pdlhcontadero-coder/AdquisiciondeDatos/Diseño 3D - Inventor/Planos Finales Sistema de Monitoreo/Planos en imagen/004 Plano 4 - Módulo de Conductividad (Tapa).jpg

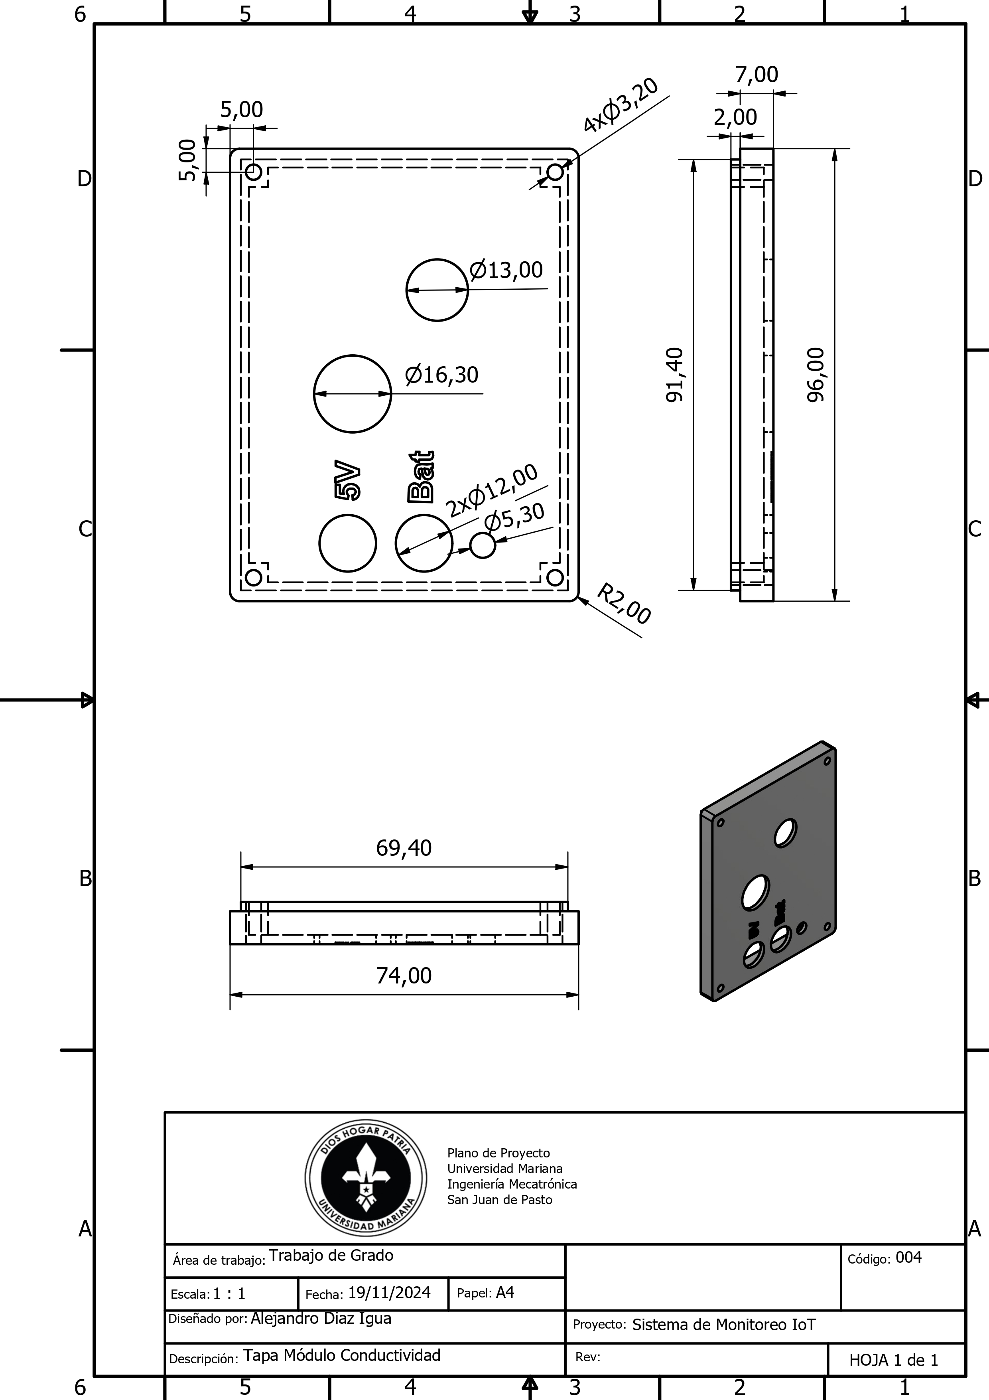
Diseño 3D - Inventor/Planos Finales Sistema de Monitoreo/Planos en imagen/004 Plano 4 - Módulo de Conductividad (Tapa).jpg
