pdlhcontadero-coder/AdquisiciondeDatos/Diseño 3D - Inventor/Planos Finales Sistema de Monitoreo/Planos en imagen/005 Plano 5 - Módulo de pH (Caja).jpg

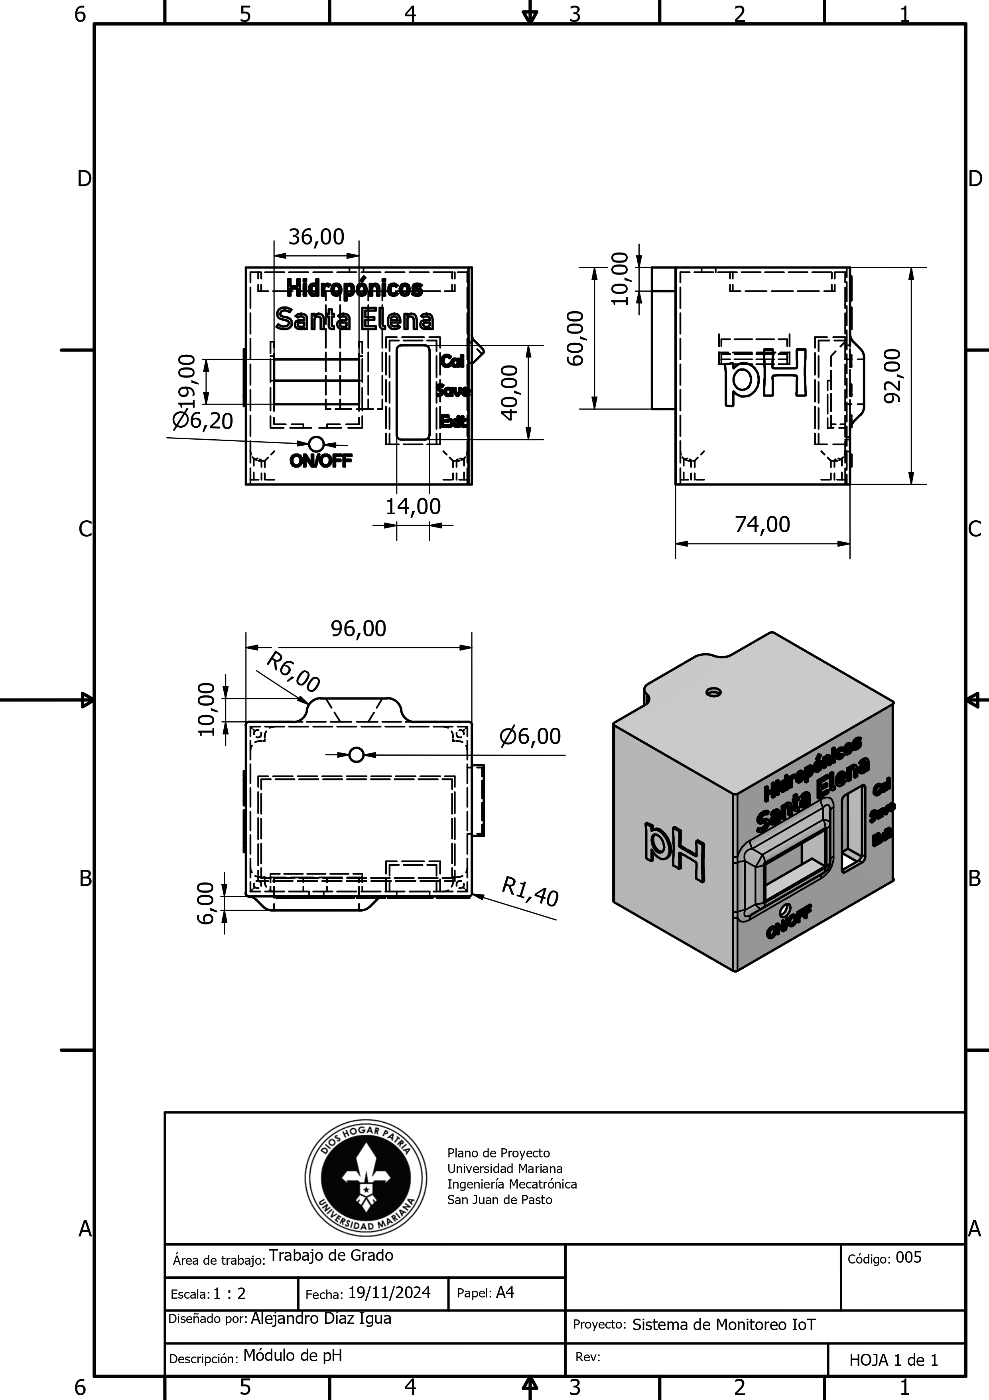
Diseño 3D - Inventor/Planos Finales Sistema de Monitoreo/Planos en imagen/005 Plano 5 - Módulo de pH (Caja).jpg
