pdlhcontadero-coder/AdquisiciondeDatos/Diseño 3D - Inventor/Planos Finales Sistema de Monitoreo/Planos en imagen/007 Plano 7 - Módulo de Nivel de Tanque (Caja).jpg

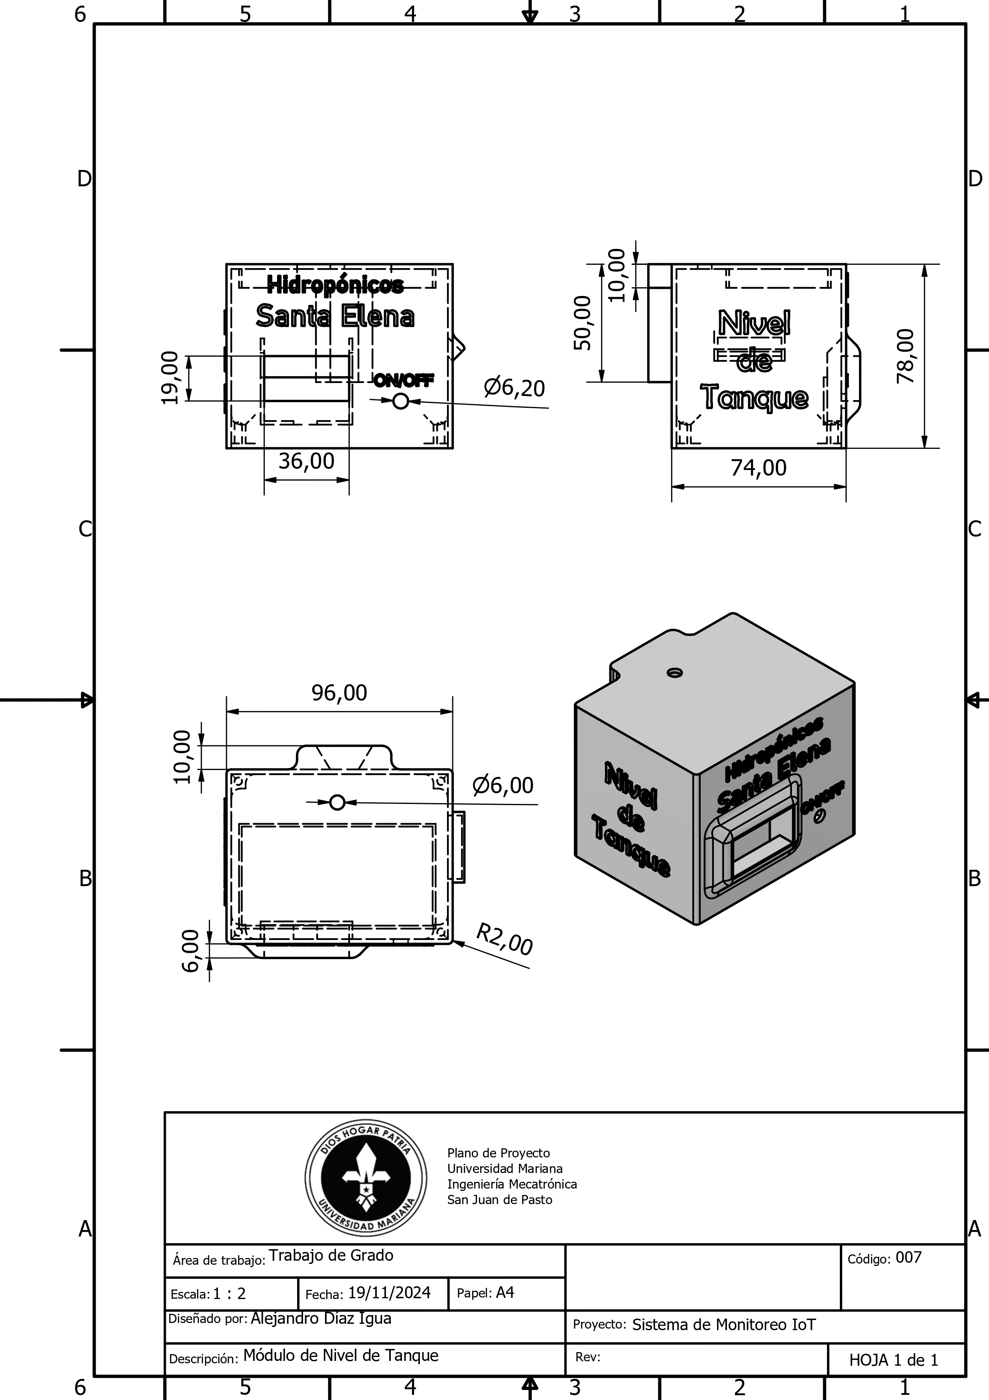
Diseño 3D - Inventor/Planos Finales Sistema de Monitoreo/Planos en imagen/007 Plano 7 - Módulo de Nivel de Tanque (Caja).jpg
