pdlhcontadero-coder/AdquisiciondeDatos/Diseño 3D - Inventor/Planos Finales Sistema de Monitoreo/Planos en imagen/008 Plano 8 - Módulo de Nivel de Tanque (Tapa).jpg

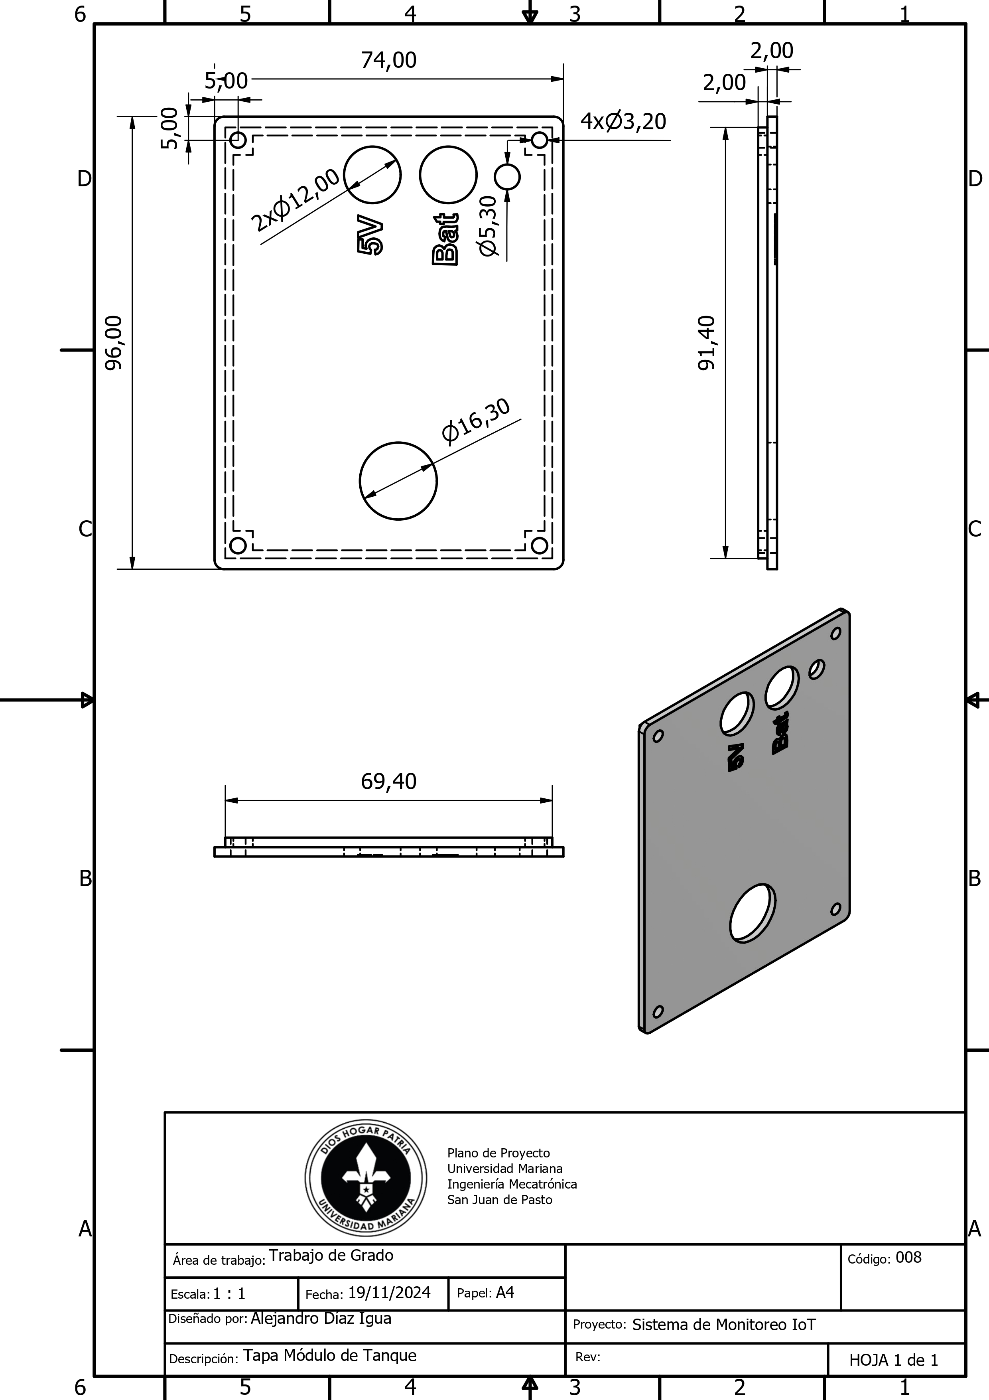
Diseño 3D - Inventor/Planos Finales Sistema de Monitoreo/Planos en imagen/008 Plano 8 - Módulo de Nivel de Tanque (Tapa).jpg
