pdlhcontadero-coder/AdquisiciondeDatos/Diseño 3D - Inventor/Planos Finales Sistema de Monitoreo/Planos en imagen/012 Plano 12 - Soporte Panel Solar 1.jpg

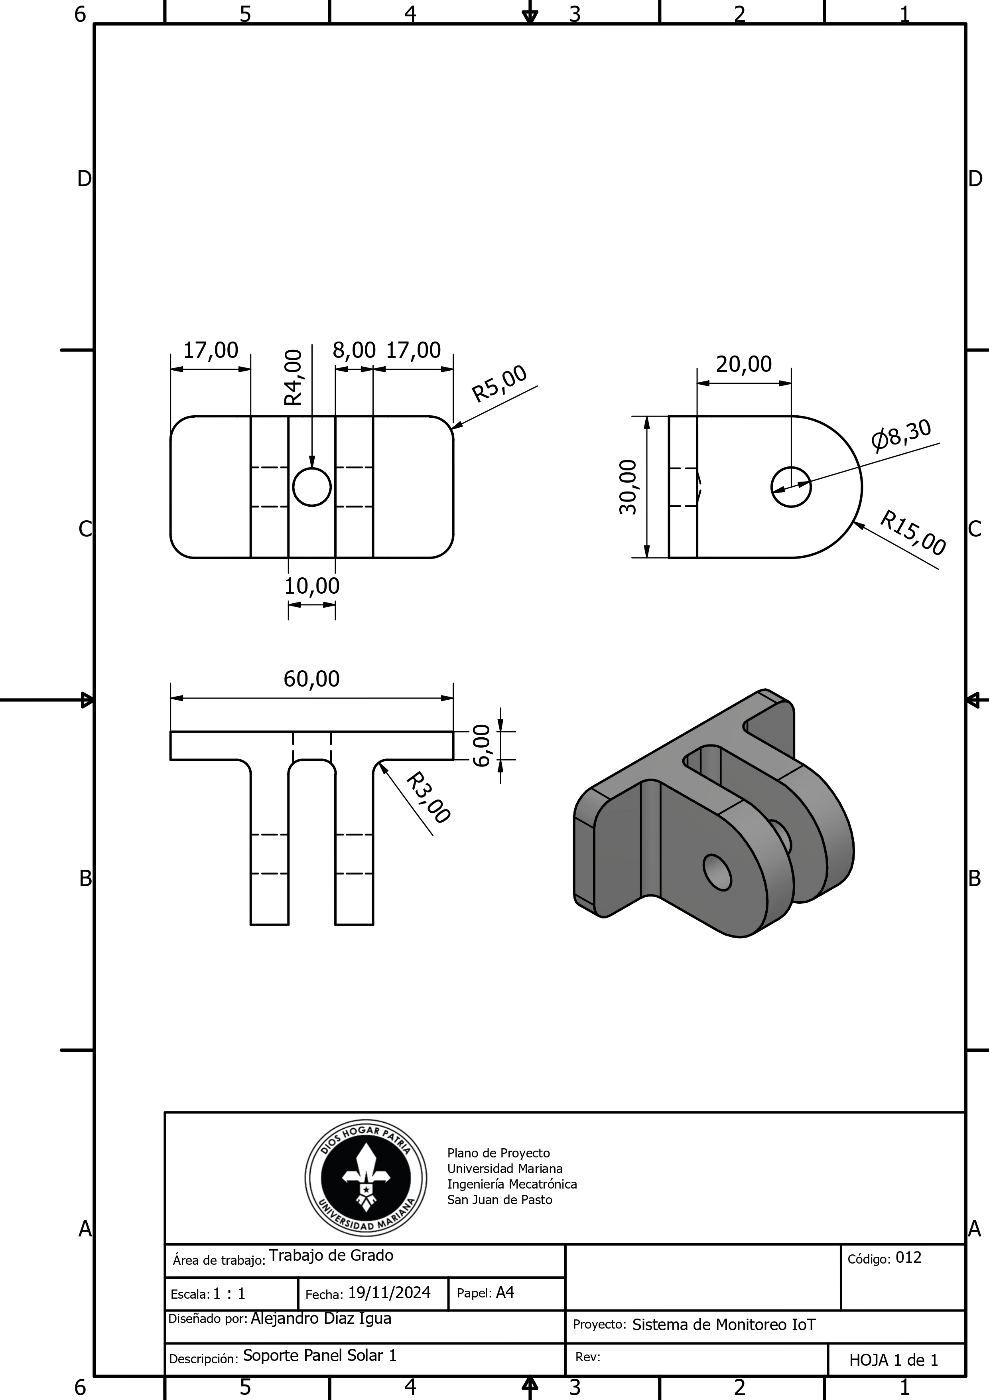
Diseño 3D - Inventor/Planos Finales Sistema de Monitoreo/Planos en imagen/012 Plano 12 - Soporte Panel Solar 1.jpg
