pdlhcontadero-coder/AdquisiciondeDatos/Diseño 3D - Inventor/Planos Finales Sistema de Monitoreo/Planos en imagen/013 Plano 13 - Soporte Panel Solar 2.jpg

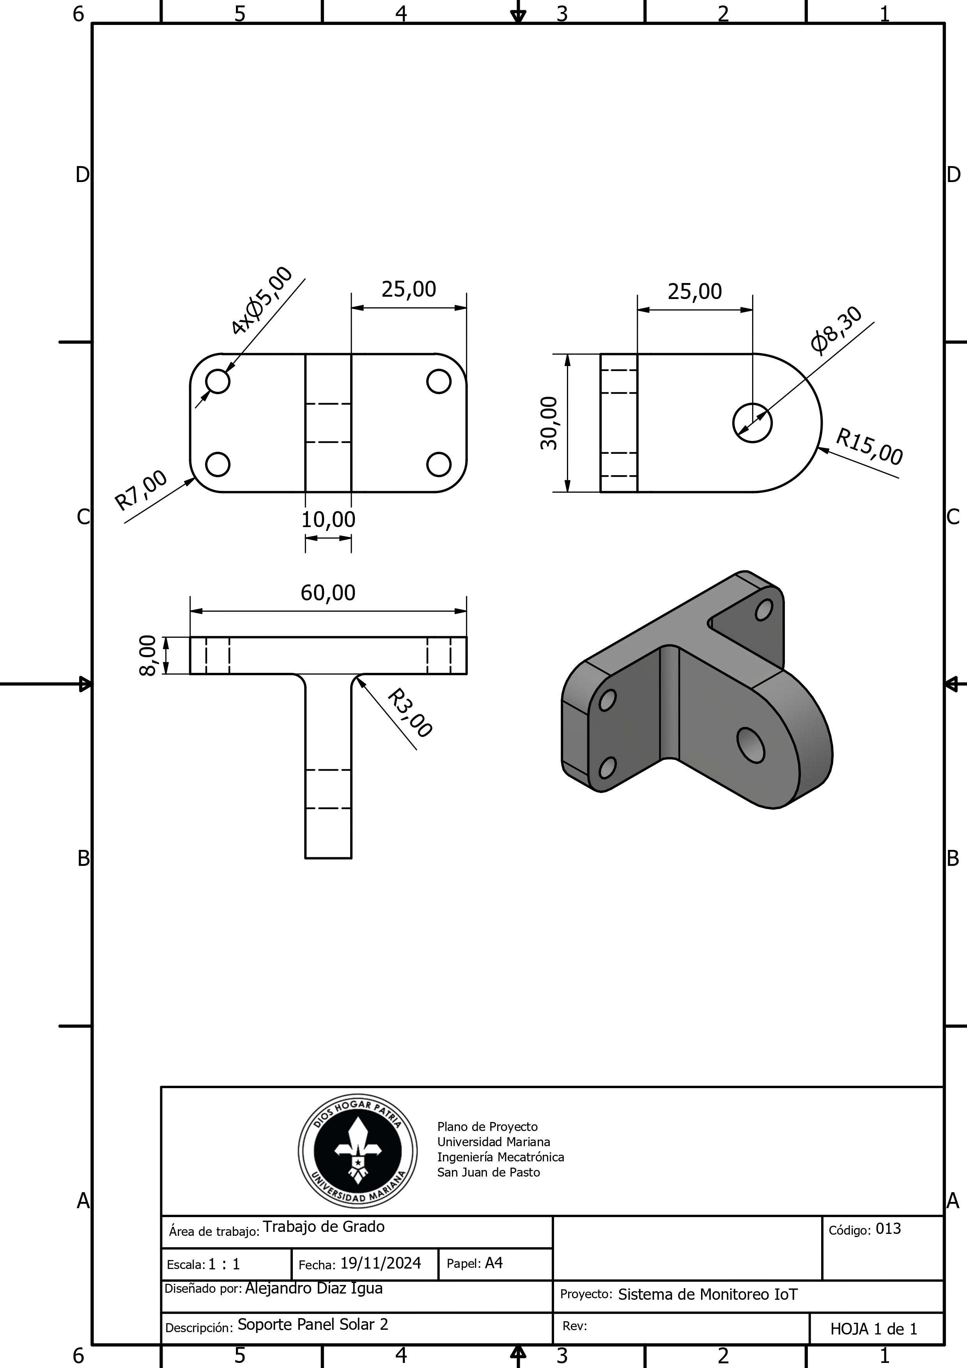
Diseño 3D - Inventor/Planos Finales Sistema de Monitoreo/Planos en imagen/013 Plano 13 - Soporte Panel Solar 2.jpg
