pdlhcontadero-coder/AdquisiciondeDatos/Diseño 3D - Inventor/Planos Finales Sistema de Monitoreo/Planos en imagen/014 Plano 14 - Botón.jpg

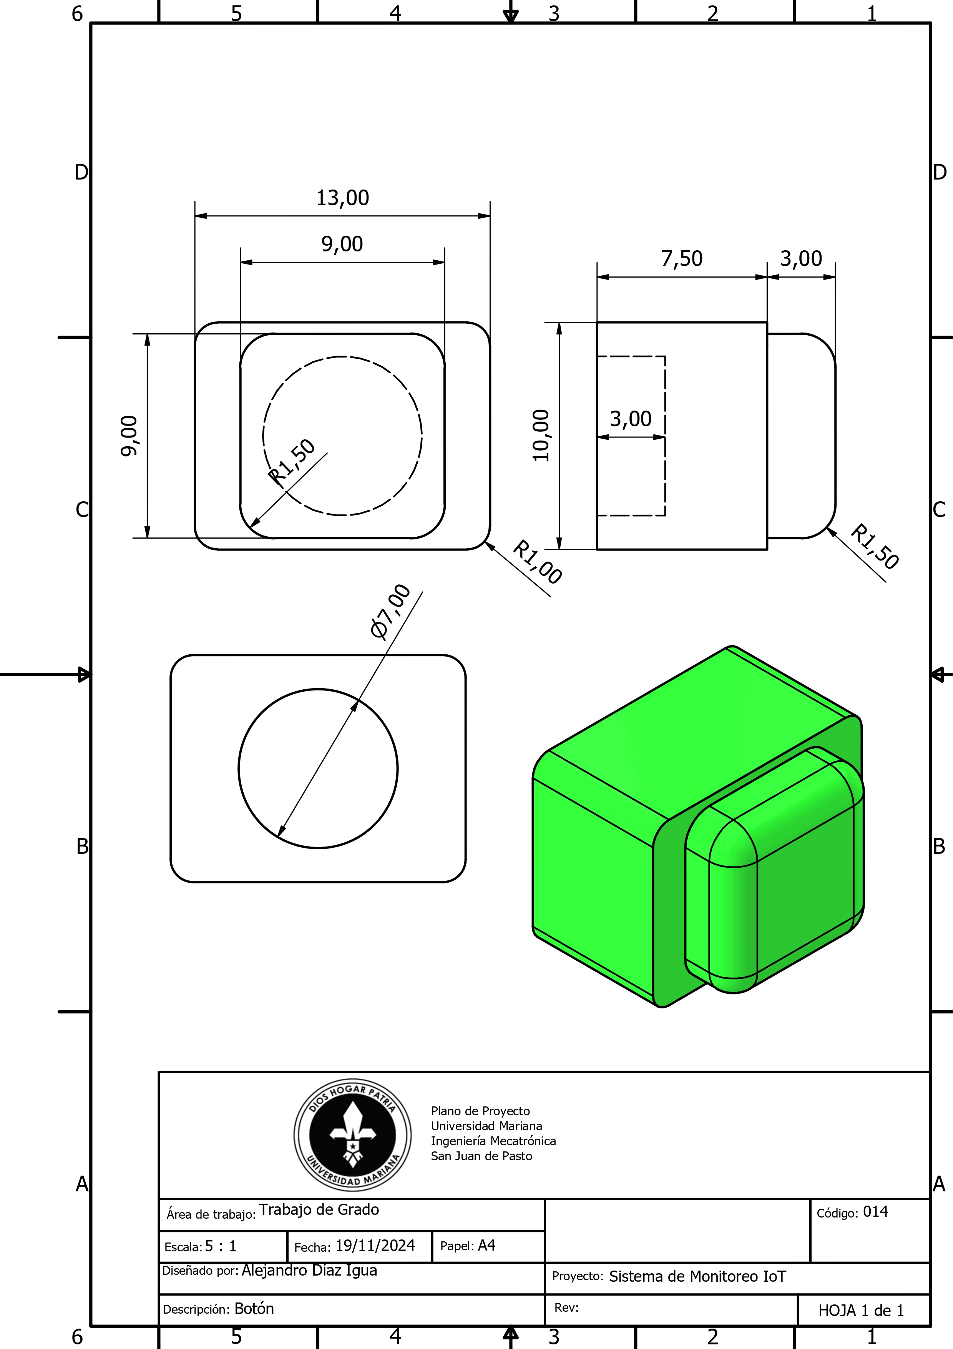
Diseño 3D - Inventor/Planos Finales Sistema de Monitoreo/Planos en imagen/014 Plano 14 - Botón.jpg
