pdlhcontadero-coder/AdquisiciondeDatos/Diseño 3D - Inventor/Planos Finales Sistema de Monitoreo/Planos en imagen/015 Plano 15 - Agarradera Módulo Principal.jpg

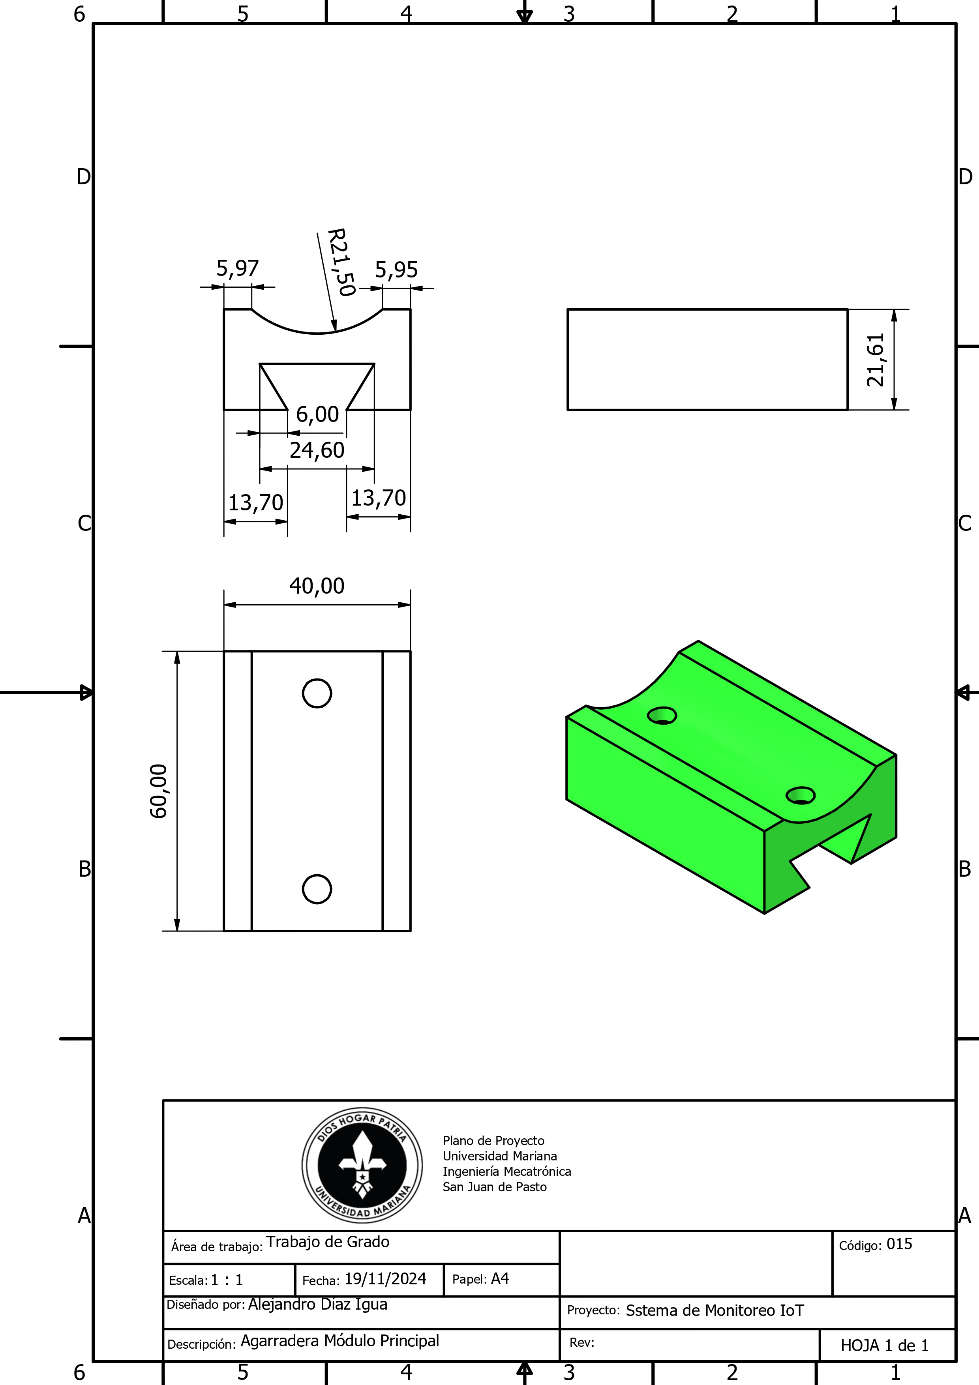
Diseño 3D - Inventor/Planos Finales Sistema de Monitoreo/Planos en imagen/015 Plano 15 - Agarradera Módulo Principal.jpg
