pdlhcontadero-coder/AdquisiciondeDatos/Diseño 3D - Inventor/Planos Finales Sistema de Monitoreo/Planos en imagen/016 Plano 16 - Agarradera 1.jpg

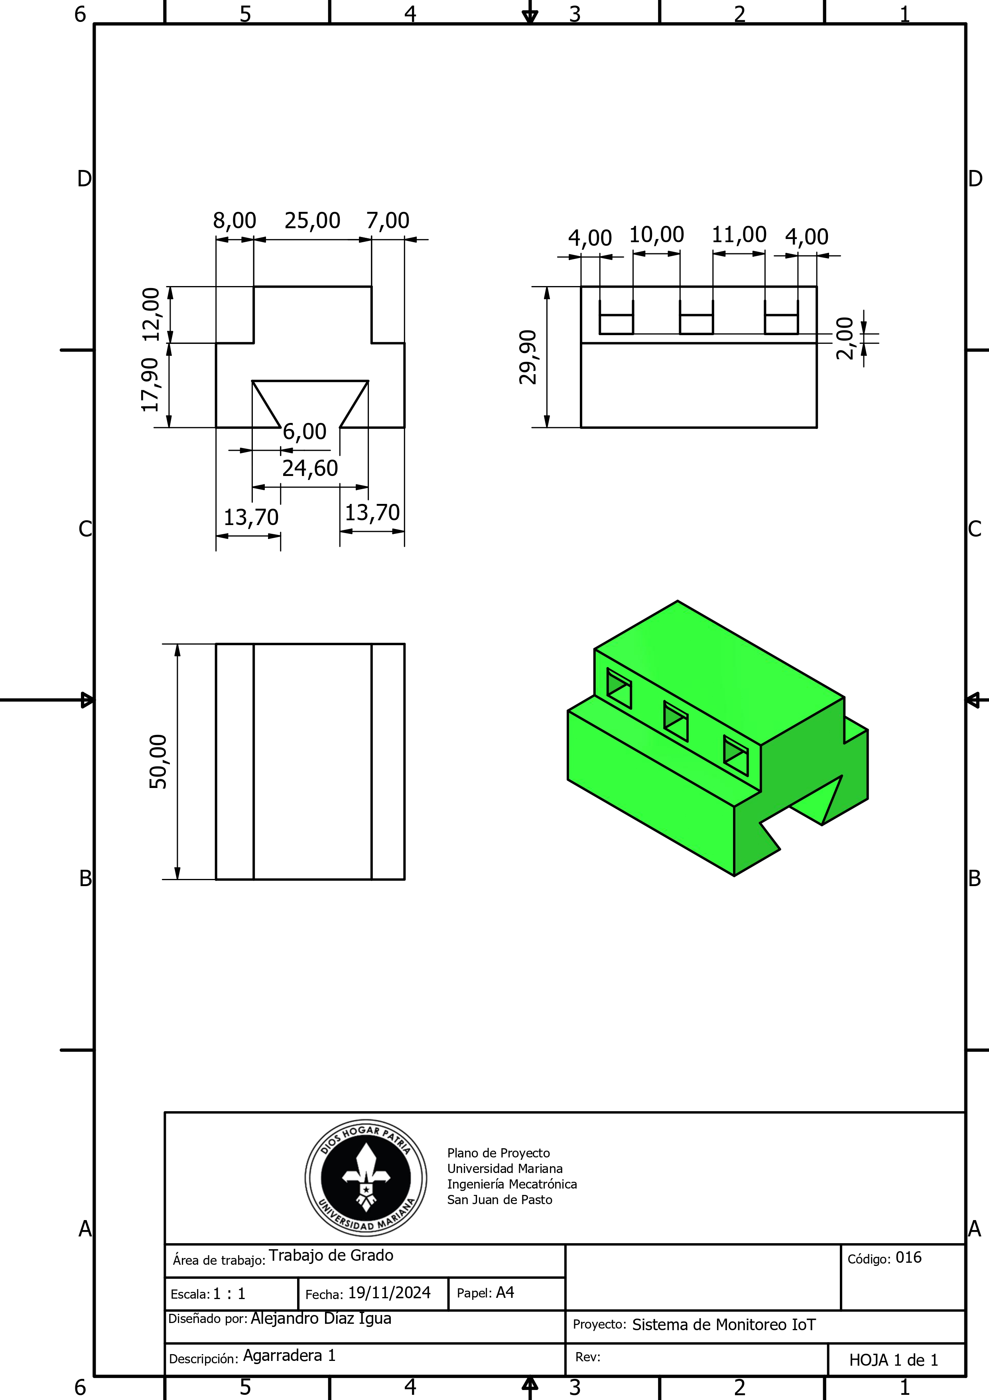
Diseño 3D - Inventor/Planos Finales Sistema de Monitoreo/Planos en imagen/016 Plano 16 - Agarradera 1.jpg
