pdlhcontadero-coder/AdquisiciondeDatos/Diseño 3D - Inventor/Planos Finales Sistema de Monitoreo/Planos en imagen/018 Plano 18 - Adapatador Sensor de Altura.jpg

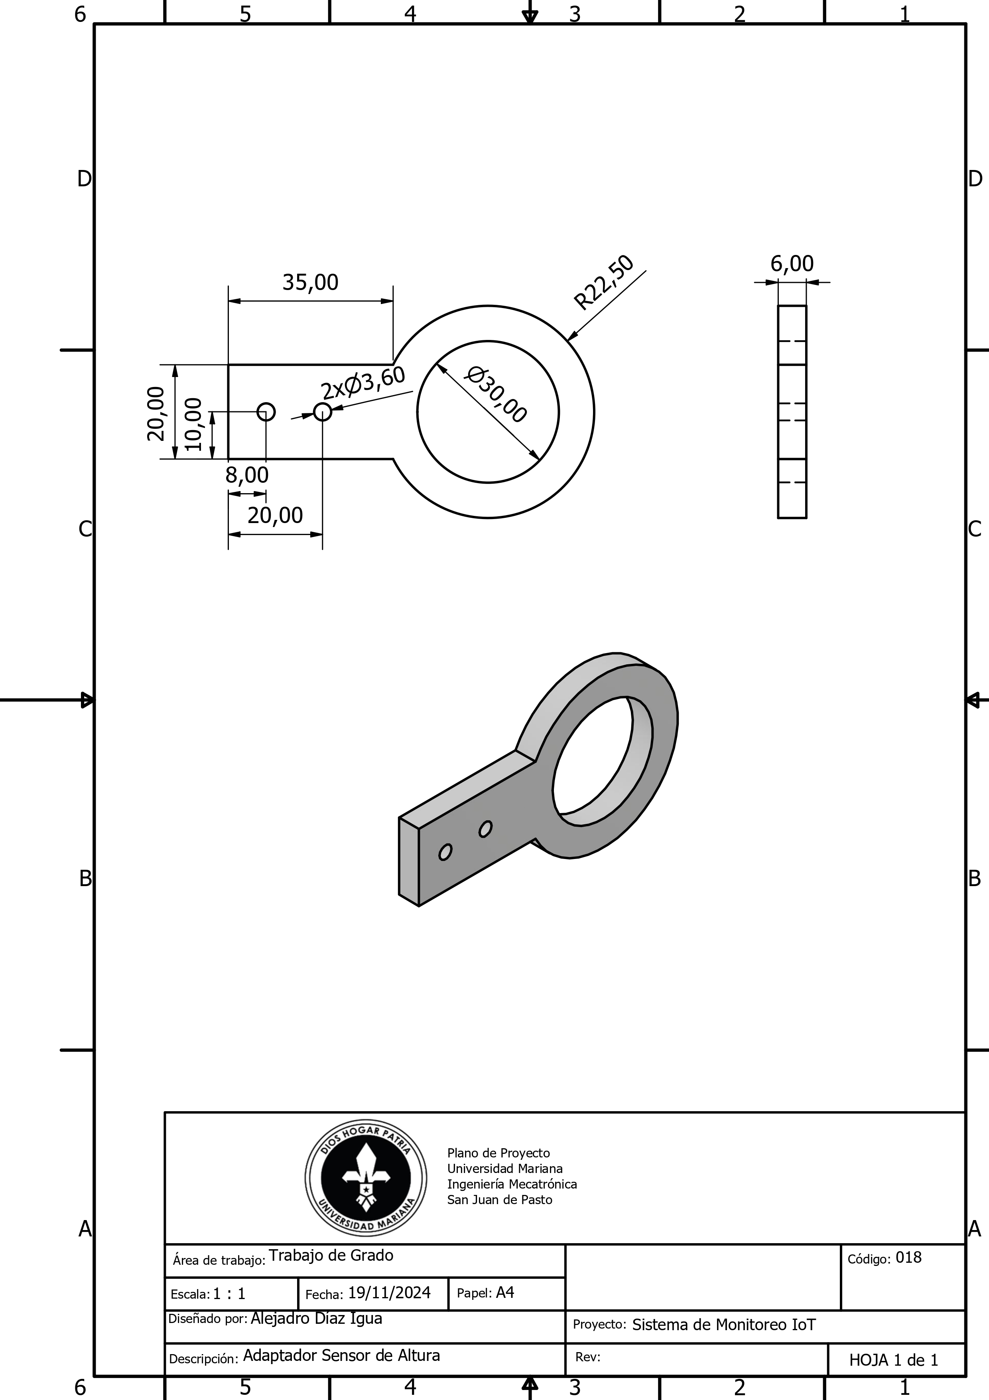
Diseño 3D - Inventor/Planos Finales Sistema de Monitoreo/Planos en imagen/018 Plano 18 - Adapatador Sensor de Altura.jpg
