pdlhcontadero-coder/AdquisiciondeDatos/Diseño 3D - Inventor/Invernadero/Ensamble/Ensamblaje1 ([Principal]).pdf

setPageBoxes("Crop", 0, 0, [0,2000,2000,0]);

TÍTULO N.º DE PIEZA | Ensamblaje1 REVISIÓN DISEÑADOR | PAVILION INGENIERO NOTAS

LA INFORMACIÓN O LOS MATERIALES DE ESTE DOCUMENTO SON PROPIEDAD E INFORMACIÓN RESTRINGIDA O MATERIALES DEL AUTOR. ESTA INFORMACIÓN NO SE PUEDE UTILIZAR, REPRODUCIR, PUBLICAR O REVELAR A TERCEROS SIN AUTORIZACIÓN POR ESCRITO. DEBE UTILIZARSE SOLO PARA LA FABRICACIÓN DE LOS ELEMENTOS ESPECIFICADOS EN EL DOCUMENTO.
