pdlhcontadero-coder/AdquisiciondeDatos/Diseño 3D - Inventor/Planos Finales Sistema de Monitoreo/018 Plano 18 - Adapatador Sensor de Altura.pdf

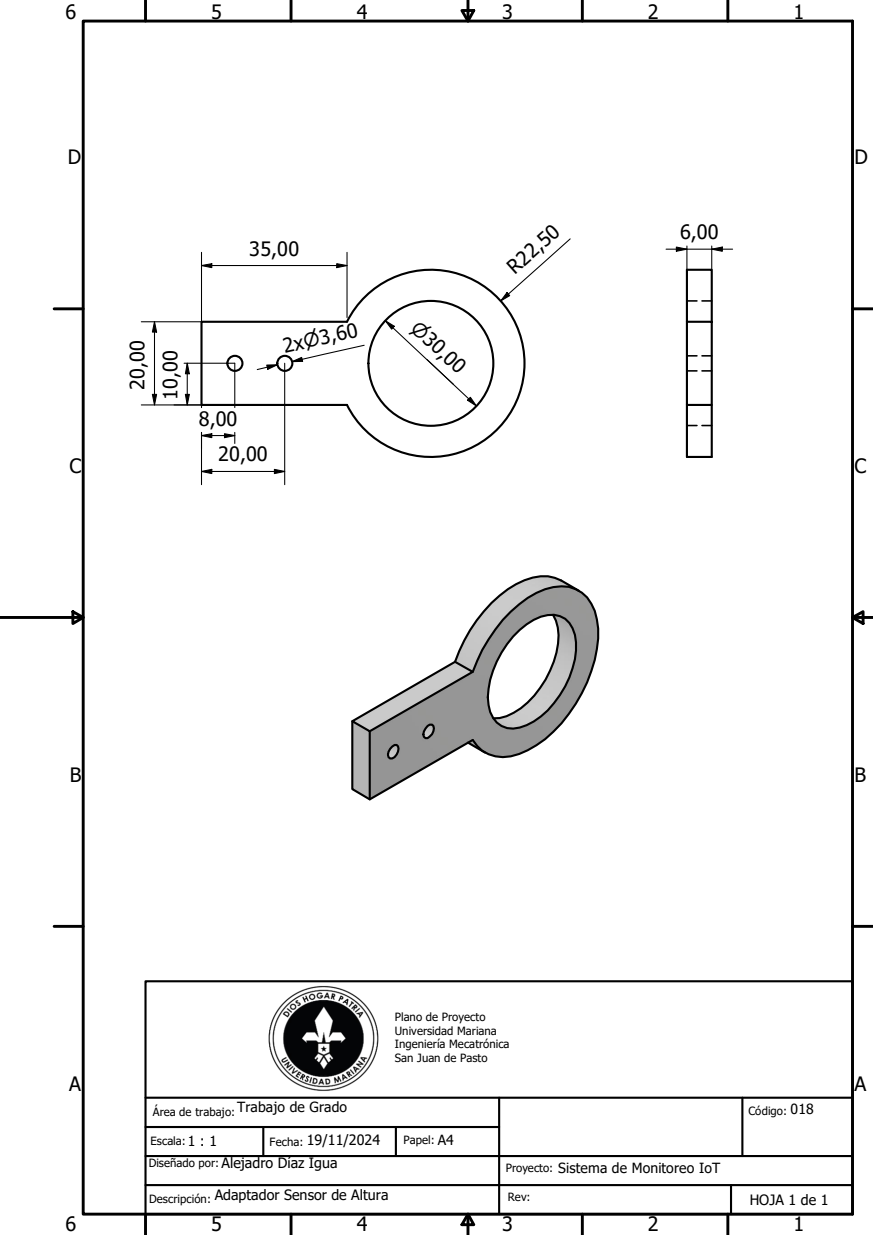
[picture p29: page 1]

Plano de Proyecto
Universidad Mariana
Ingeniería Mecatrónica
San Juan de Pasto

Área de trabajo: Trabajo de Grado | | Código: 018

Escala: 1 : 1 | Fecha: 19/11/2024 | Papel: A4
Diseñado por: Alejadro Díaz Igua | Proyecto: Sistema de Monitoreo IoT

Descripción: Adaptador Sensor de Altura | Rev: | HOJA 1 de 1
