pdlhcontadero-coder/AdquisiciondeDatos/Diseño 3D - Inventor/Planos Finales Sistema de Monitoreo/013 Plano 13 - Soporte Panel Solar 2.pdf

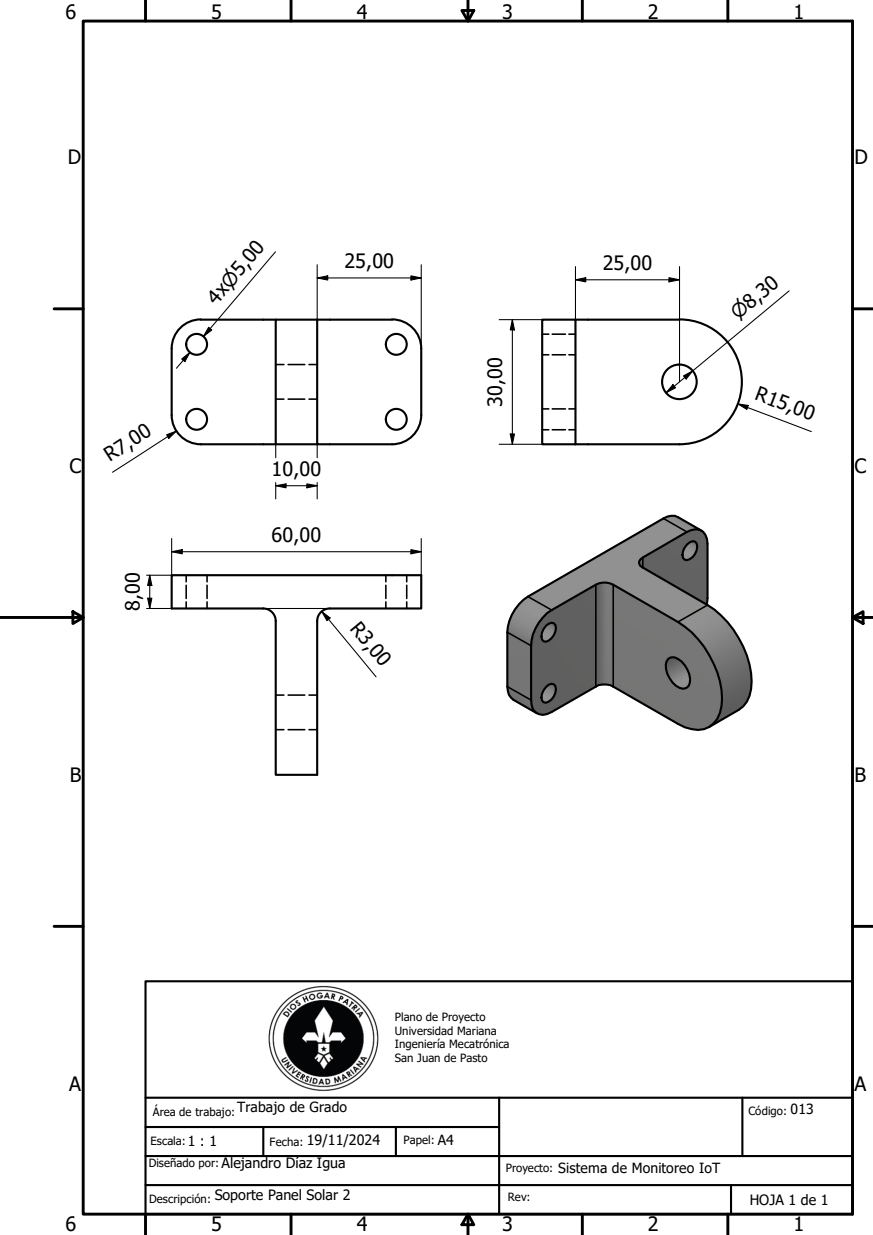
[picture p42: page 1]

Plano de Proyecto
Universidad Mariana
Ingeniería Mecatrónica
San Juan de Pasto

Área de trabajo: Trabajo de Grado | | Código: 013

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

Descripción: Soporte Panel Solar 2 | Rev: | HOJA 1 de 1
