pdlhcontadero-coder/AdquisiciondeDatos/Diseño 3D - Inventor/Planos Finales Sistema de Monitoreo/014 Plano 14 - Botón.pdf

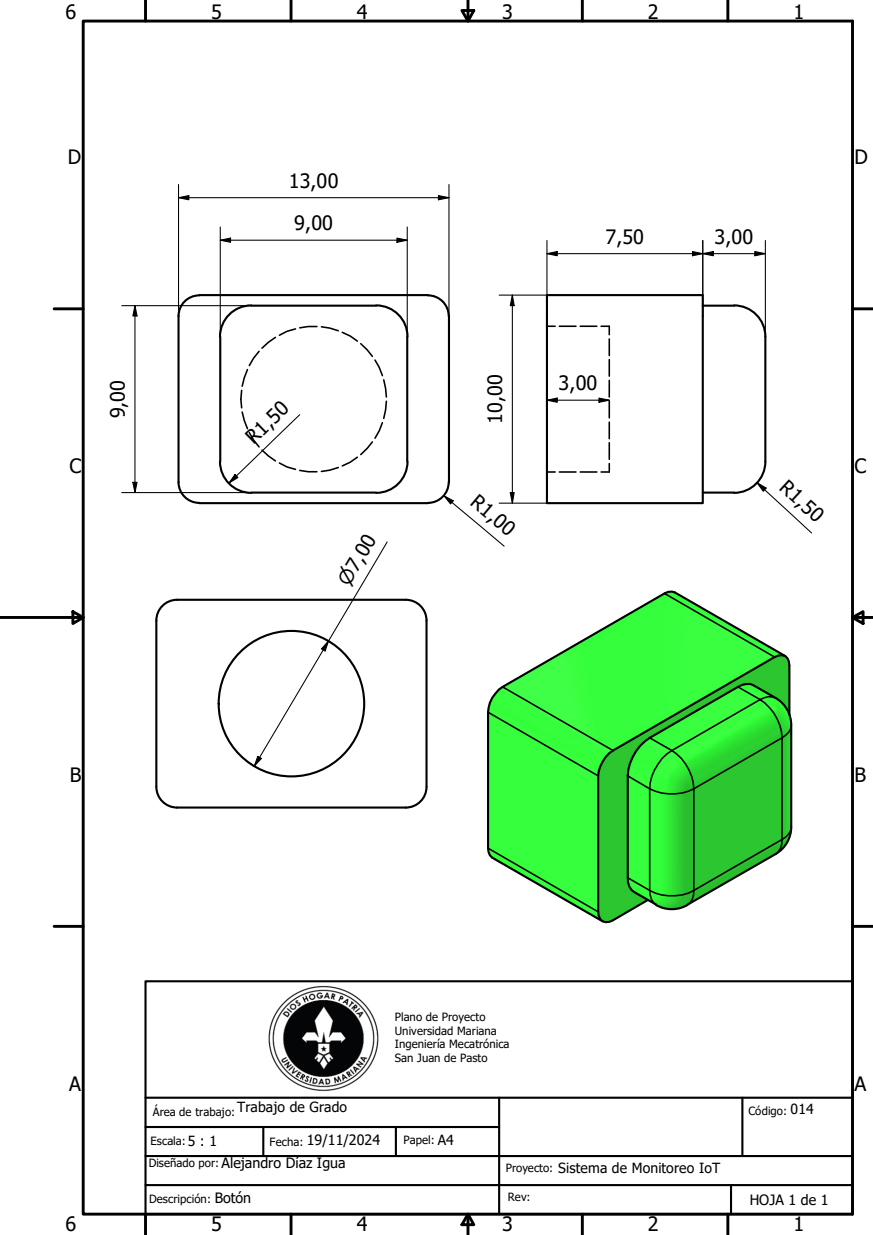
[picture p43: page 1]

Plano de Proyecto
Universidad Mariana
Ingeniería Mecatrónica
San Juan de Pasto

Área de trabajo: Trabajo de Grado | | Código: 014

Escala: 5 : 1 | Fecha: 19/11/2024 | Papel: A4
Diseñado por: Alejandro Díaz Igua | Proyecto: Sistema de Monitoreo IoT

Descripción: Botón | Rev: | HOJA 1 de 1
