pdlhcontadero-coder/AdquisiciondeDatos/Diseño 3D - Inventor/Planos Finales Sistema de Monitoreo/015 Plano 15 - Agarradera Módulo Principal.pdf

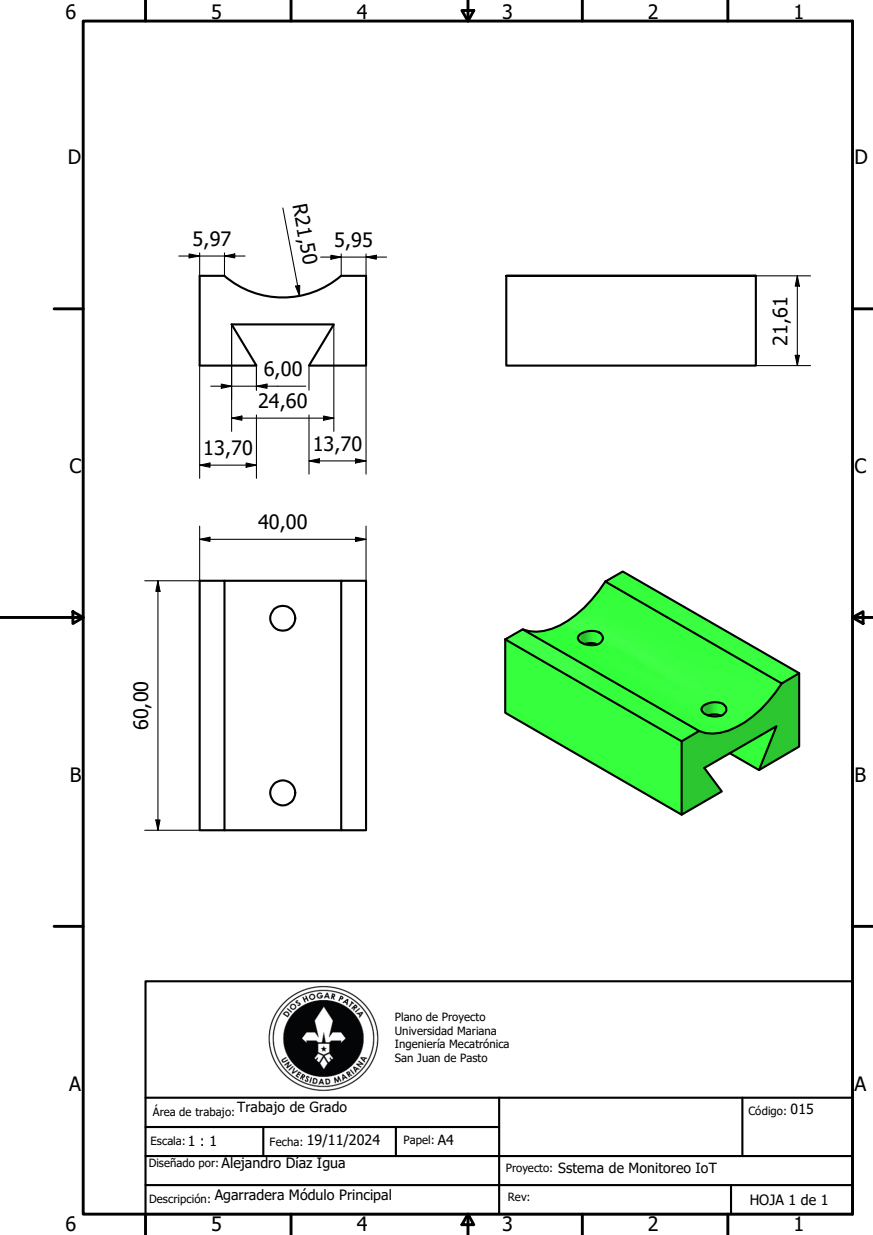
[picture p44: page 1]

Plano de Proyecto
Universidad Mariana
Ingeniería Mecatrónica
San Juan de Pasto

Área de trabajo: Trabajo de Grado | | Código: 015

Escala: 1 : 1 | Fecha: 19/11/2024 | Papel: A4
Diseñado por: Alejandro Díaz Igua | Proyecto: Sstema de Monitoreo IoT

Descripción: Agarradera Módulo Principal | Rev: | HOJA 1 de 1
