pdlhcontadero-coder/AdquisiciondeDatos/Diseño 3D - Inventor/Planos Finales Sistema de Monitoreo/016 Plano 16 - Agarradera 1.pdf

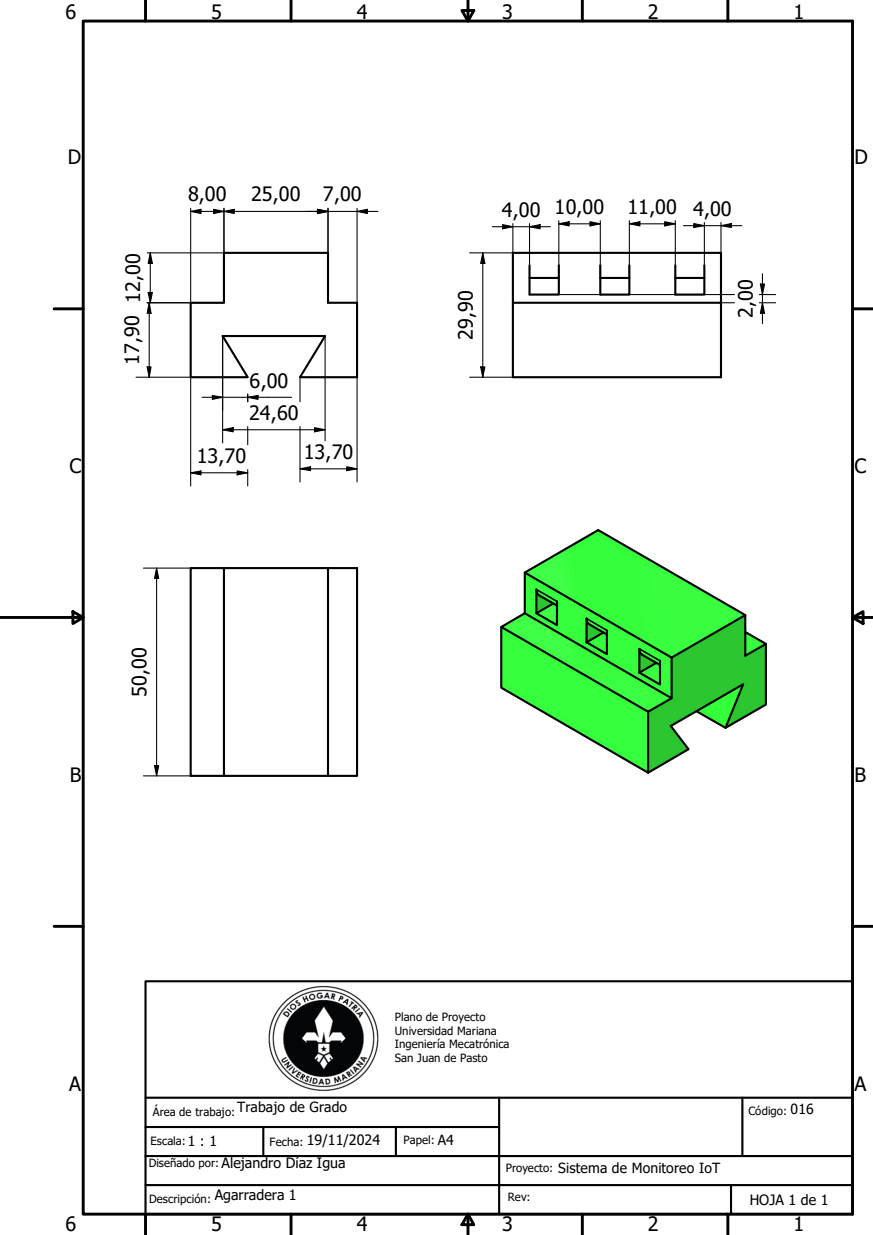
[picture p45: page 1]

Plano de Proyecto
Universidad Mariana
Ingeniería Mecatrónica
San Juan de Pasto

Área de trabajo: Trabajo de Grado | | Código: 016

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

Descripción: Agarradera 1 | Rev: | HOJA 1 de 1
