pdlhcontadero-coder/AdquisiciondeDatos/Diseño 3D - Inventor/Planos Finales Sistema de Monitoreo/017 Plano 17 - Agarradera 2.pdf

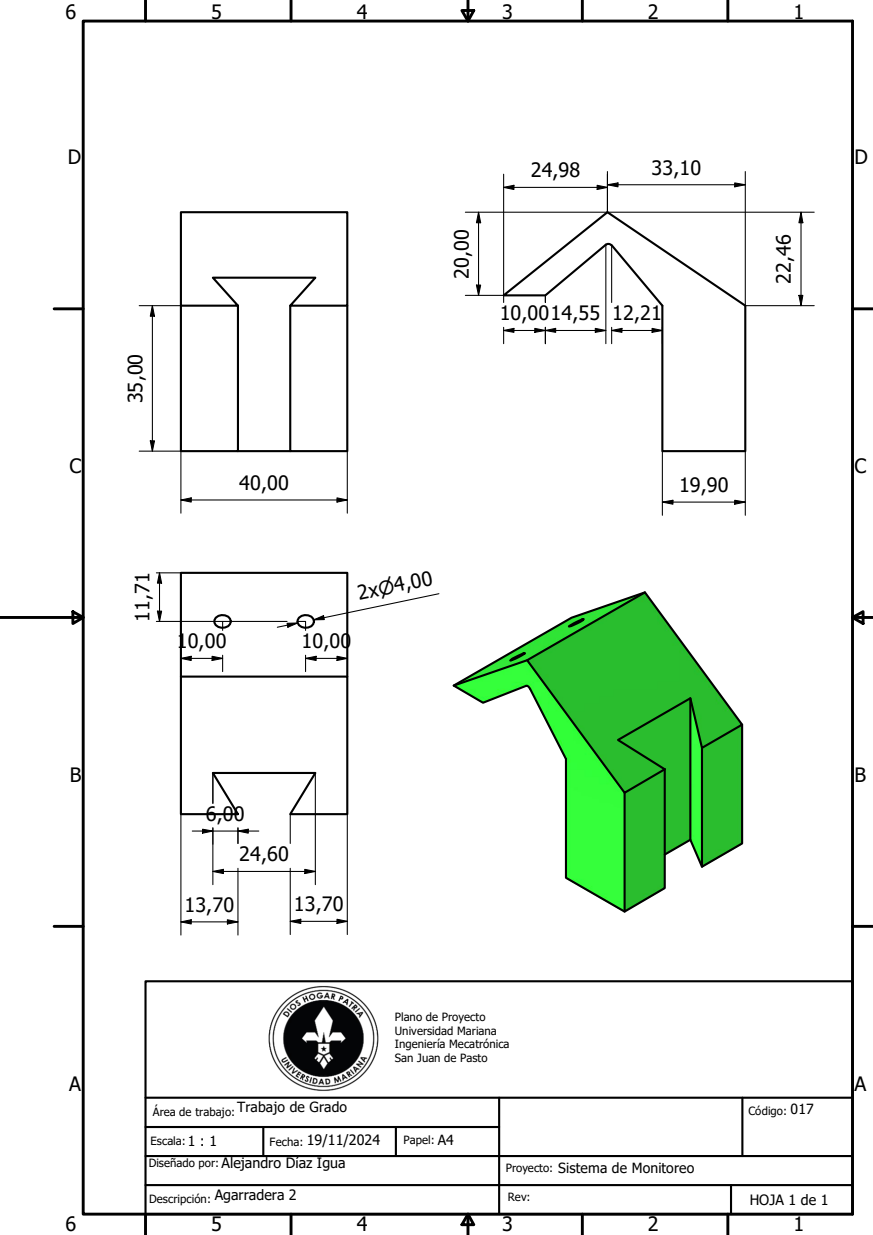
[picture p46: page 1]

Plano de Proyecto
Universidad Mariana
Ingeniería Mecatrónica
San Juan de Pasto

Área de trabajo: Trabajo de Grado | | Código: 017

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

Descripción: Agarradera 2 | Rev: | HOJA 1 de 1
