pdlhcontadero-coder/AdquisiciondeDatos/Diseño 3D - Inventor/Planos Finales Sistema de Monitoreo/Planos Sistema de Monitoreo.pdf

D | D

HOJA 1 de 1; Área de trabajo:; Trabajo de Grado; Escala:; Fecha:; Papel:; Rev:; Descripción:; Módulo Principal

Plano de Proyecto
Universidad Mariana
Ingeniería Mecatrónica
San Juan de Pasto

Código: 001

Diseñado por: Alejandro Díaz Igua

Proyecto: Sistema de Monitoreo IoT

D | 142,30 | D

12,00

Código:

Plano de Proyecto
Universidad Mariana
Ingeniería Mecatrónica
San Juan de Pasto

Área de trabajo: Proyecto de Grado

Descripción: Tapa Módulo Principal

D | D
36,00 | 14,00

Código:

Plano de Proyecto
Universidad Mariana
Ingeniería Mecatrónica
San Juan de Pasto

Área de trabajo: Trabajo de Grado

Descripción: Módulo de Conductividad

D | 5

D

Código:

Plano de Proyecto
Universidad Mariana
Ingeniería Mecatrónica
San Juan de Pasto

Área de trabajo: Trabajo de Grado

Diseñado por: Alejandro Diaz Igua

Descripción: Tapa Módulo Conductividad

D | D

36,00

Código:

Plano de Proyecto
Universidad Mariana
Ingeniería Mecatrónica
San Juan de Pasto

Área de trabajo: Trabajo de Grado

Descripción: Módulo de pH

D | 5

D

Código:

Plano de Proyecto
Universidad Mariana
Ingeniería Mecatrónica
San Juan de Pasto

Área de trabajo: Trabajo de Grado

Diseñado por: Alejandro Diaz Igua

Descripción: Tapa Módulo pH

D | D

Código:

Plano de Proyecto
Universidad Mariana
Ingeniería Mecatrónica
San Juan de Pasto

Área de trabajo: Trabajo de Grado

Descripción: Módulo de Nivel de Tanque

D | D

74,00

Código:

Plano de Proyecto
Universidad Mariana
Ingeniería Mecatrónica
San Juan de Pasto

Área de trabajo: Trabajo de Grado

Descripción: Tapa Módulo de Tanque

D | D

Código:

Plano de Proyecto
Universidad Mariana
Ingeniería Mecatrónica
San Juan de Pasto

Área de trabajo: Trabajo de Grado

Descripción: Módulo de Nivel de Agua

D | D

74,00

Código:

Plano de Proyecto
Universidad Mariana
Ingeniería Mecatrónica
San Juan de Pasto

Área de trabajo: Trabajo de Grado

Proyecto: Sistema de Monitoreo

Descripción: Tapa Módulo de Nivel

D | D

138,30

Código:

Plano de Proyecto
Universidad Mariana
Ingeniería Mecatrónica
San Juan de Pasto

Área de trabajo: Trabajo de Grado

Descripción: Base Panel Solar

D | D

8,00 17,00

Código:

Plano de Proyecto
Universidad Mariana
Ingeniería Mecatrónica
San Juan de Pasto

Área de trabajo: Trabajo de Grado

Descripción: Soporte Panel Solar 1

D | D

25,00

Código:

Plano de Proyecto
Universidad Mariana
Ingeniería Mecatrónica
San Juan de Pasto

Área de trabajo: Trabajo de Grado

Descripción: Soporte Panel Solar 2

D | D
7,50 | 3,00

Código:; Descripción: Botón

Plano de Proyecto
Universidad Mariana
Ingeniería Mecatrónica
San Juan de Pasto

Área de trabajo: Trabajo de Grado

D | D
5,97 | 5,95

Código:

Plano de Proyecto
Universidad Mariana
Ingeniería Mecatrónica
San Juan de Pasto

Área de trabajo: Trabajo de Grado

Proyecto: Sstema de Monitoreo IoT

Descripción: Agarradera Módulo Principal

D | D
8,00 | 25,00 7,00

Código:; Descripción: Agarradera 1

Plano de Proyecto
Universidad Mariana
Ingeniería Mecatrónica
San Juan de Pasto

Área de trabajo: Trabajo de Grado

D | D
10,0014,55 | 12,21

Código:; Descripción: Agarradera 2

Plano de Proyecto
Universidad Mariana
Ingeniería Mecatrónica
San Juan de Pasto

Área de trabajo: Trabajo de Grado

Proyecto: Sistema de Monitoreo

D | D

35,00

Código:

Plano de Proyecto
Universidad Mariana
Ingeniería Mecatrónica
San Juan de Pasto

Área de trabajo: Trabajo de Grado

Diseñado por: Alejadro Díaz Igua

Descripción: Adaptador Sensor de Altura
