pdlhcontadero-coder/AdquisiciondeDatos/Diseño 3D - Inventor/Planos/Agarraderas/Agarradera Lateral.pdf

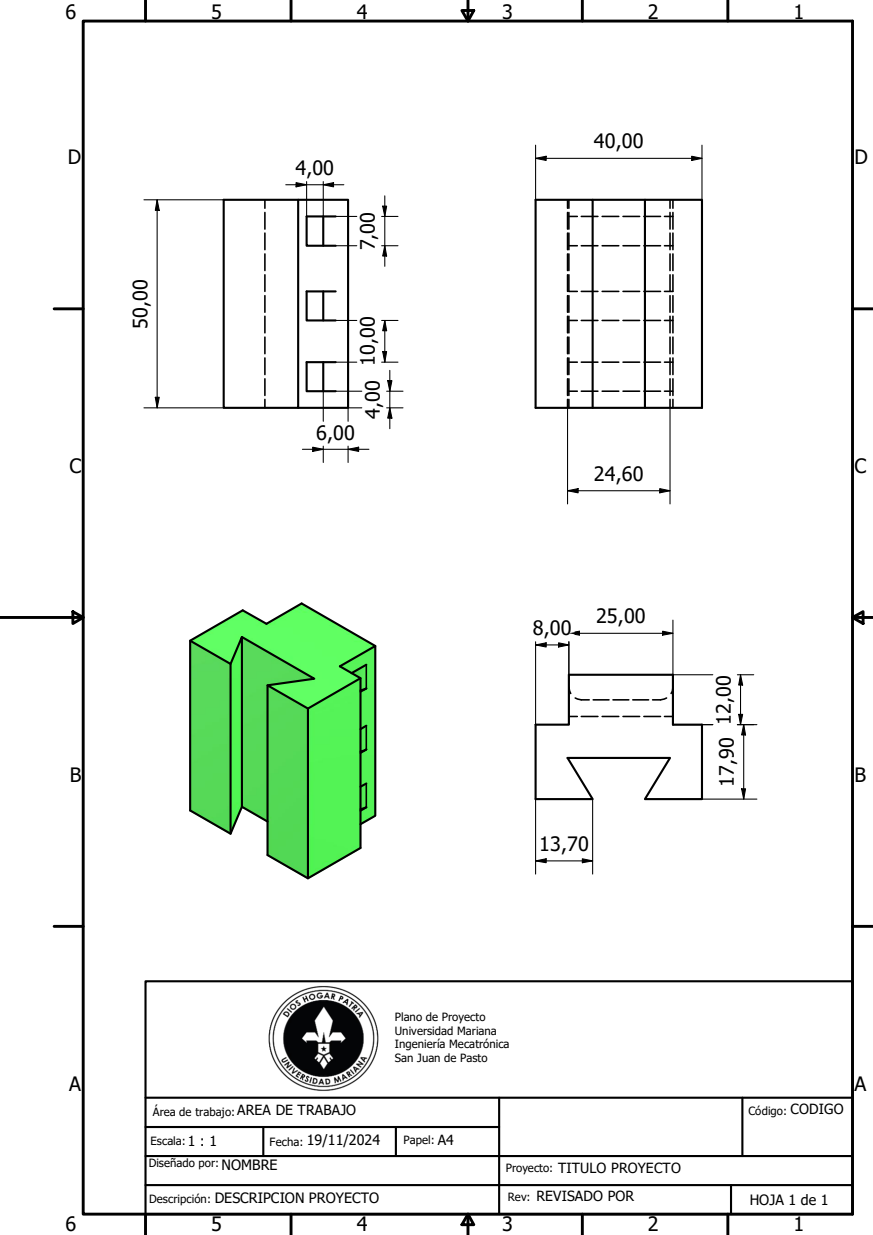
[picture p47: page 1]

Plano de Proyecto
Universidad Mariana
Ingeniería Mecatrónica
San Juan de Pasto

Área de trabajo:AREA DE TRABAJO | | Código: CODIGO

Escala: 1 : 1 | Fecha: 19/11/2024 | Papel: A4

Diseñado por:NOMBRE | Proyecto: TITULO PROYECTO

Descripción: DESCRIPCION PROYECTO | REVISADO POR Rev: | HOJA 1 de 1
